AnnikaCodes/buzzers/openclipart-vectors-button-155539.png

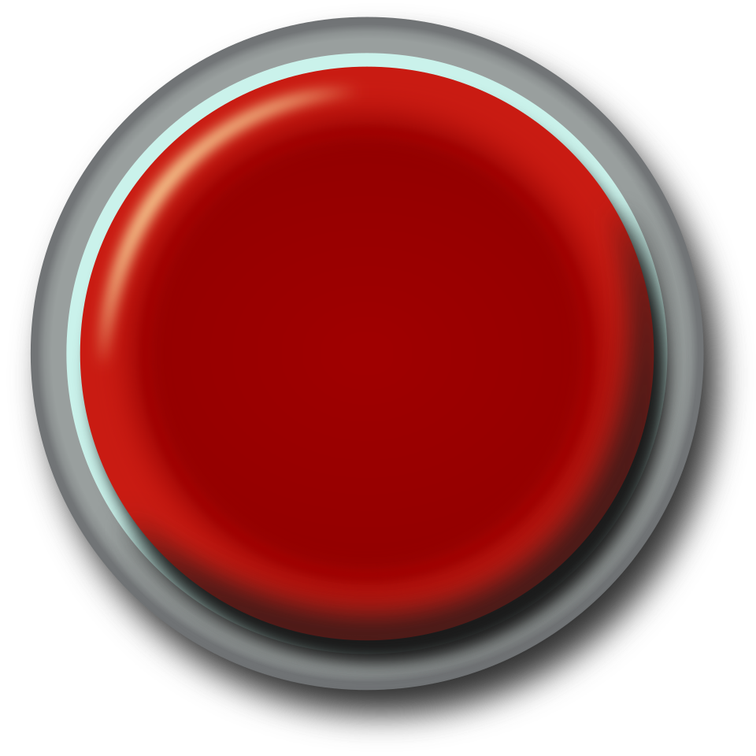
openclipart-vectors-button-155539.png
