AnnikaCodes/buzzers/Hinge box with a premounted lid (Print at once) - 1155457/images/1b6b984905737d37dba8c5a674a471ea.png

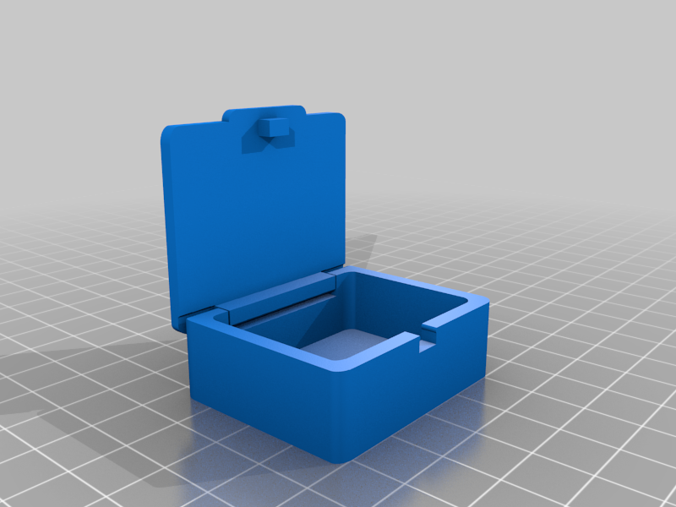
Hinge box with a premounted lid (Print at once) - 1155457/images/1b6b984905737d37dba8c5a674a471ea.png
