AnnikaCodes/buzzers/Hinge box with a premounted lid (Print at once) - 1155457/images/55-110-25.jpg

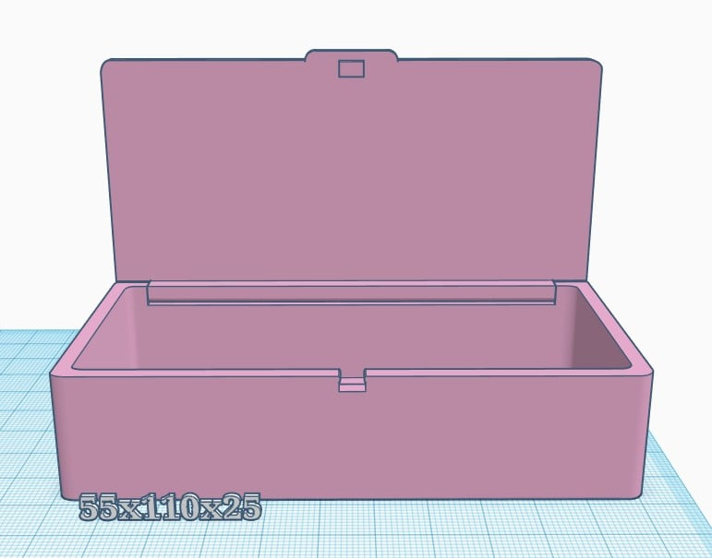
Hinge box with a premounted lid (Print at once) - 1155457/images/55-110-25.jpg
