AnnikaCodes/buzzers/Hinge box with a premounted lid (Print at once) - 1155457/images/isomet.jpg

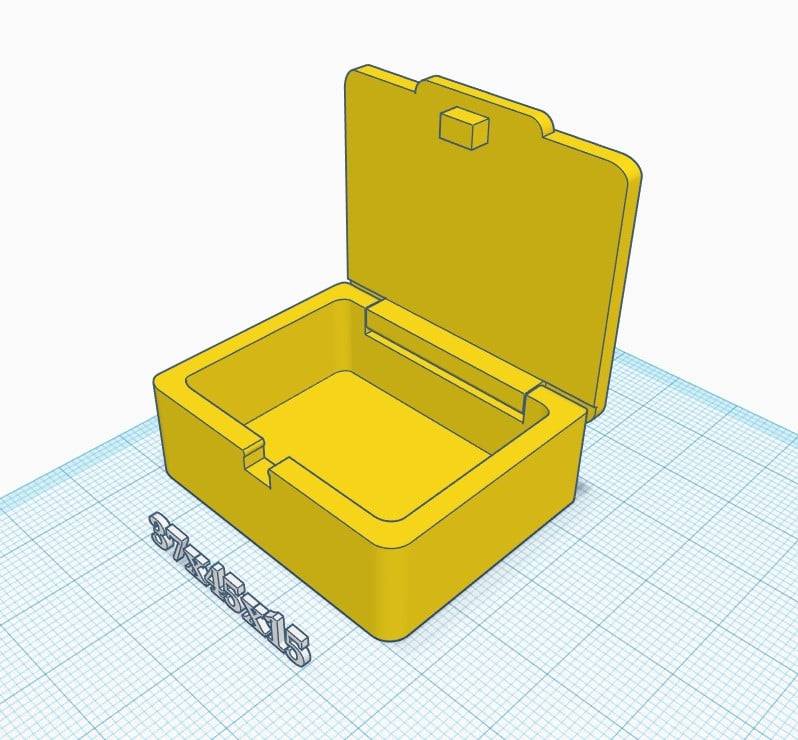
Hinge box with a premounted lid (Print at once) - 1155457/images/isomet.jpg
