AnnikaCodes/buzzers/code/circuitpython.py

import digitalio
import board
import audiomp3
import audiopwmio
CLEAR_PIN = board.GP16
# (led, switch)
RED_TEAM_PINS = [(board.GP17, board.GP16)]
GREEN_TEAM_PINS = []

clear = digitalio.DigitalInOut(CLEAR_PIN)
clear.switch_to_input(pull=digitalio.Pull.DOWN)

red_pins = [(digitalio.DigitalInOut(x), digitalio.DigitalInOut(y)) for x,y in RED_TEAM_PINS]
green_pins = [(digitalio.DigitalInOut(x), digitalio.DigitalInOut(y)) for x,y in GREEN_TEAM_PINS]
for led, switch in red_pins + green_pins:
    led.switch_to_output(value=False)
    switch.switch_to_input(pull=digitalio.Pull.DOWN)

# https://learn.adafruit.com/mp3-playback-rp2040/pico-mp3
audio = audiopwmio.PWMAudioOut(board.GP15)
buzz_tone = audiomp3.MP3Decoder(open("buzz.mp3", "rb"))

def buzzer_loop():
    while True:
        led_pin = await_buzz(red_pins, green_pins)
        led_pin.value = True
        play_buzz_tone() # todo: different tones for different teams
        await_clear()
        led_pin.value = False

def await_buzz(red, green):
    for led, switch in red + green:
        if switch.value == True:
            return led

def await_clear():
    pass

def play_buzz_tone():
    audio.play(buzz_tone)
